ThomasKlap/Rheinturmuhr-ESP-Multi-Processor/parts/Bauteile Rheinturm geschraubt NEU 2501 v16 parts - 08-Restaurant.stl

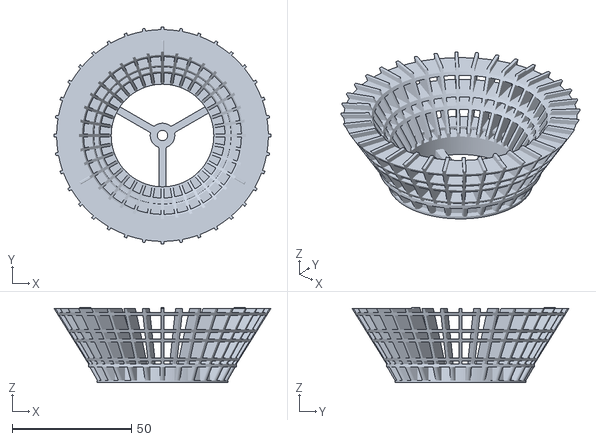
[picture p19: CAD file, 2025-09-29]
parts/Bauteile Rheinturm geschraubt NEU 2501 v16 parts - 08-Restaurant.stl
91.0 x 91.0 x 31.6
