ThomasKlap/Rheinturmuhr-ESP-Multi-Processor/parts/Bauteile Rheinturm geschraubt NEU 2501 v16 parts - 09-RestaurantWindow.stl

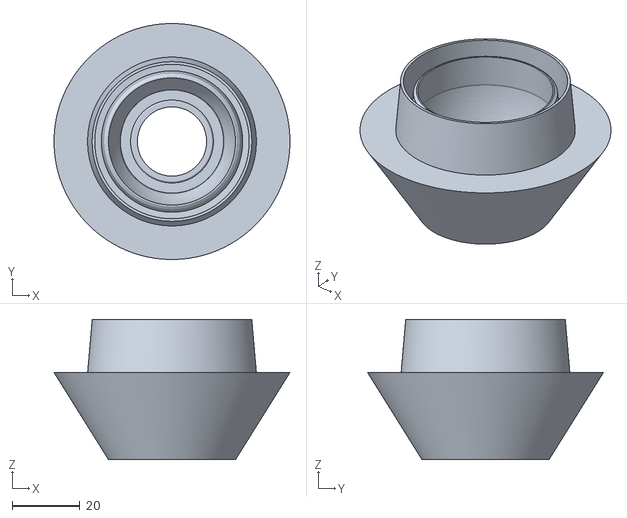
[picture p20: CAD file, 2025-09-29]
parts/Bauteile Rheinturm geschraubt NEU 2501 v16 parts - 09-RestaurantWindow.stl
69.5 x 69.5 x 41.3
