ThomasKlap/Rheinturmuhr-ESP-Multi-Processor/parts/Bauteile Rheinturm geschraubt NEU 2501 v19 - 02-Shaft-1.stl

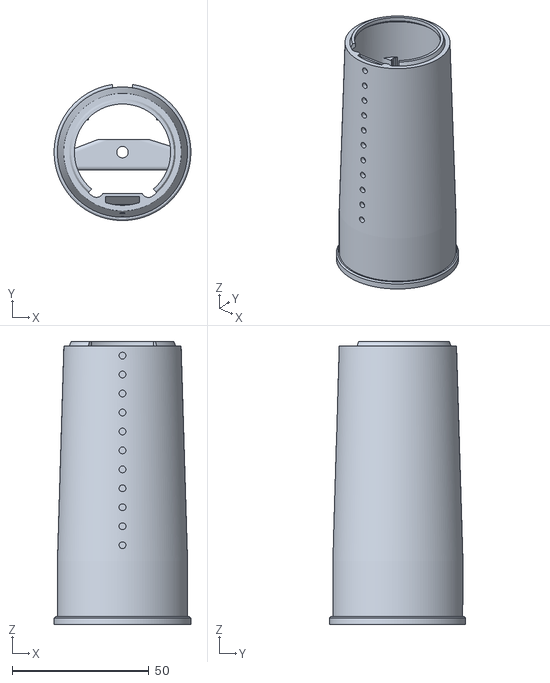
[picture p21: CAD file, 2025-09-29]
parts/Bauteile Rheinturm geschraubt NEU 2501 v19 - 02-Shaft-1.stl
50.1 x 49.8 x 103.6
